niftypsycho/ortho-40percent/images/IMG_2475.JPG

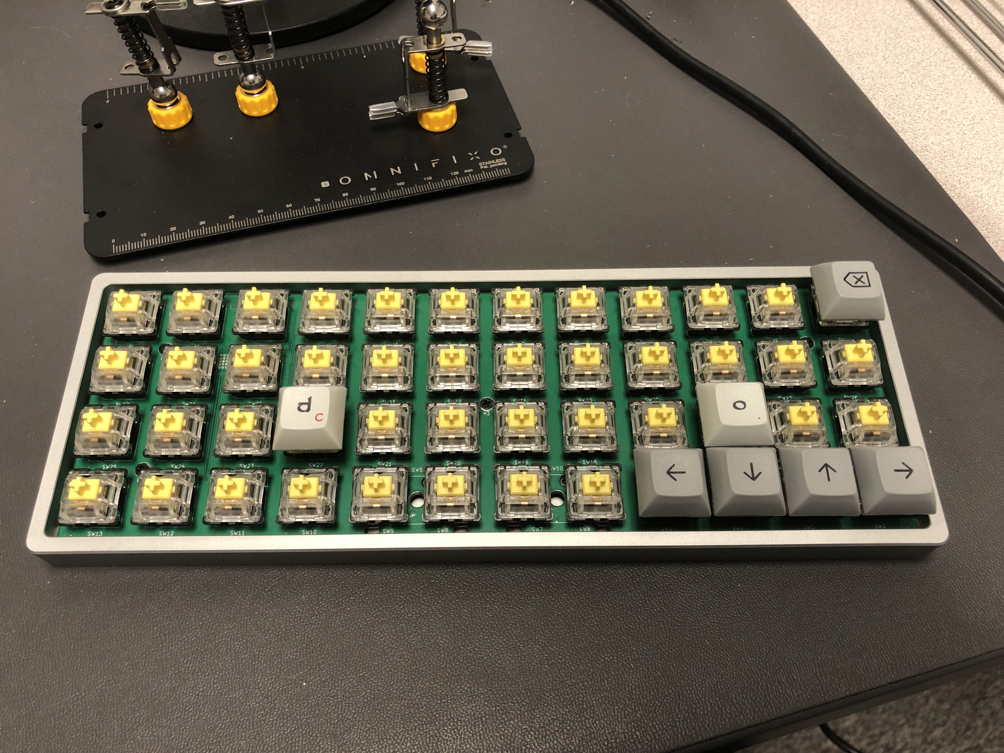
images/IMG_2475.JPG
