niftypsycho/ortho-40percent/images/IMG_2476.JPG

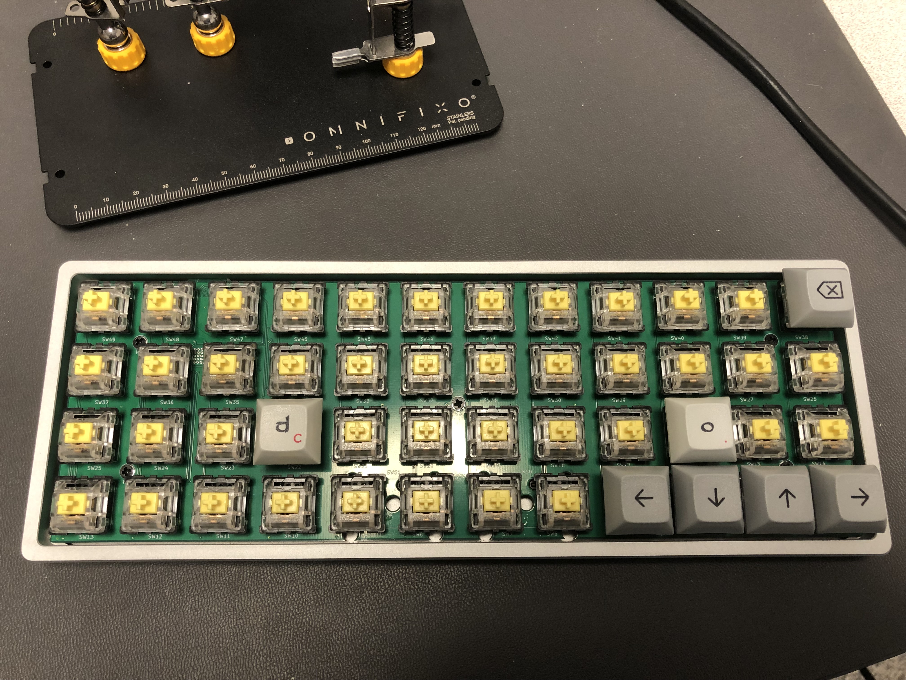
images/IMG_2476.JPG
