niftypsycho/ortho-40percent/images/IMG_2477.JPG

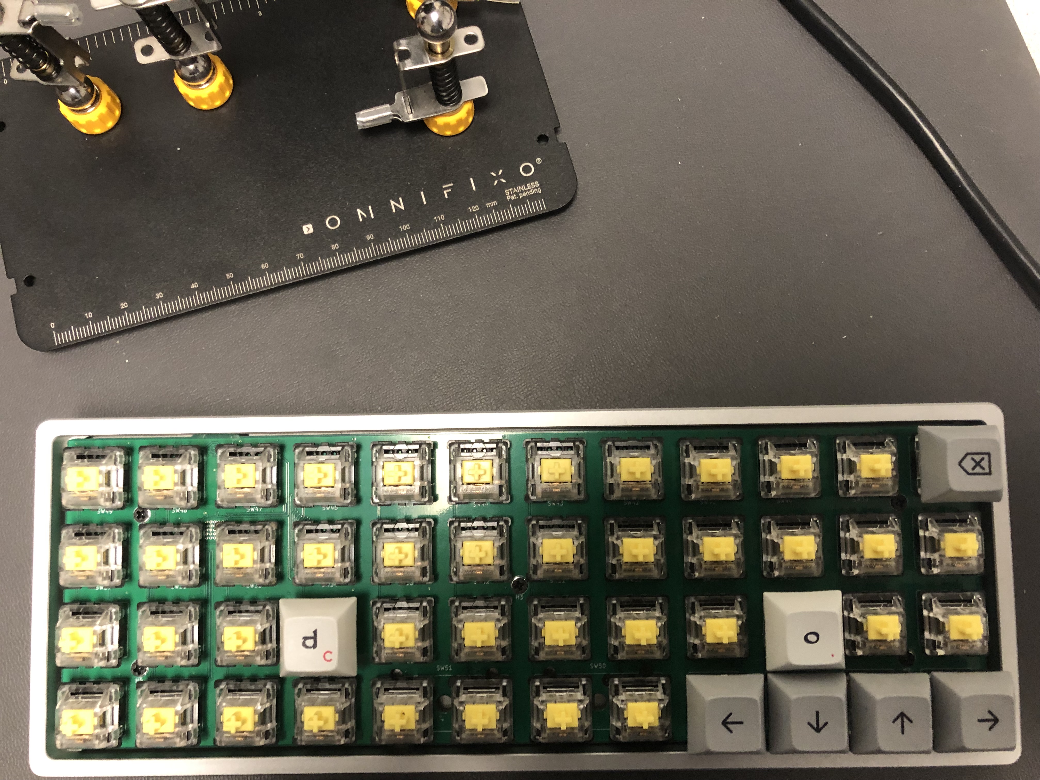
images/IMG_2477.JPG
