niftypsycho/ortho-40percent/images/IMG_2478.JPG

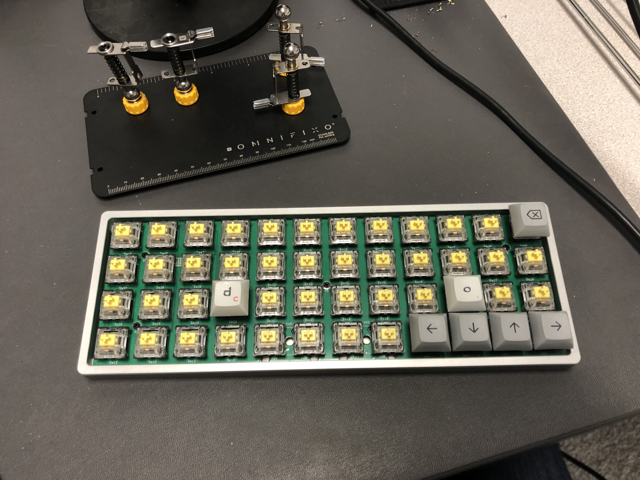
images/IMG_2478.JPG
