niftypsycho/ortho-40percent/images/IMG_2479.JPG

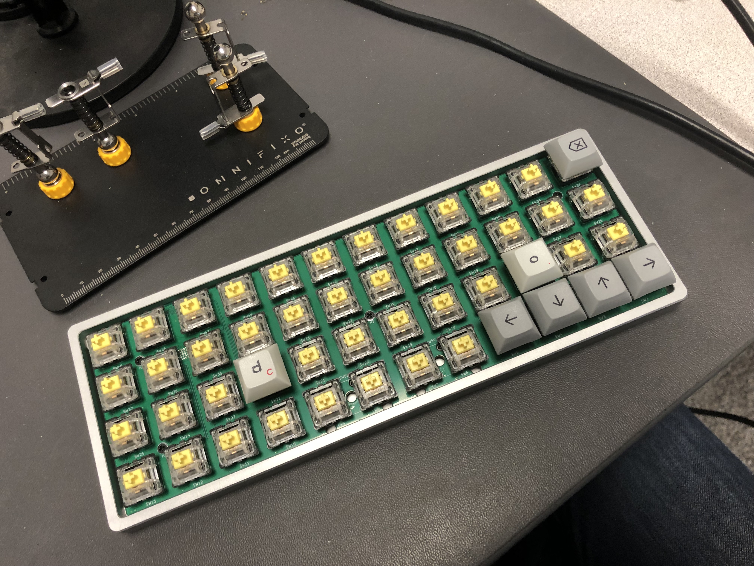
images/IMG_2479.JPG
