niftypsycho/ortho-40percent/images/IMG_2480.JPG

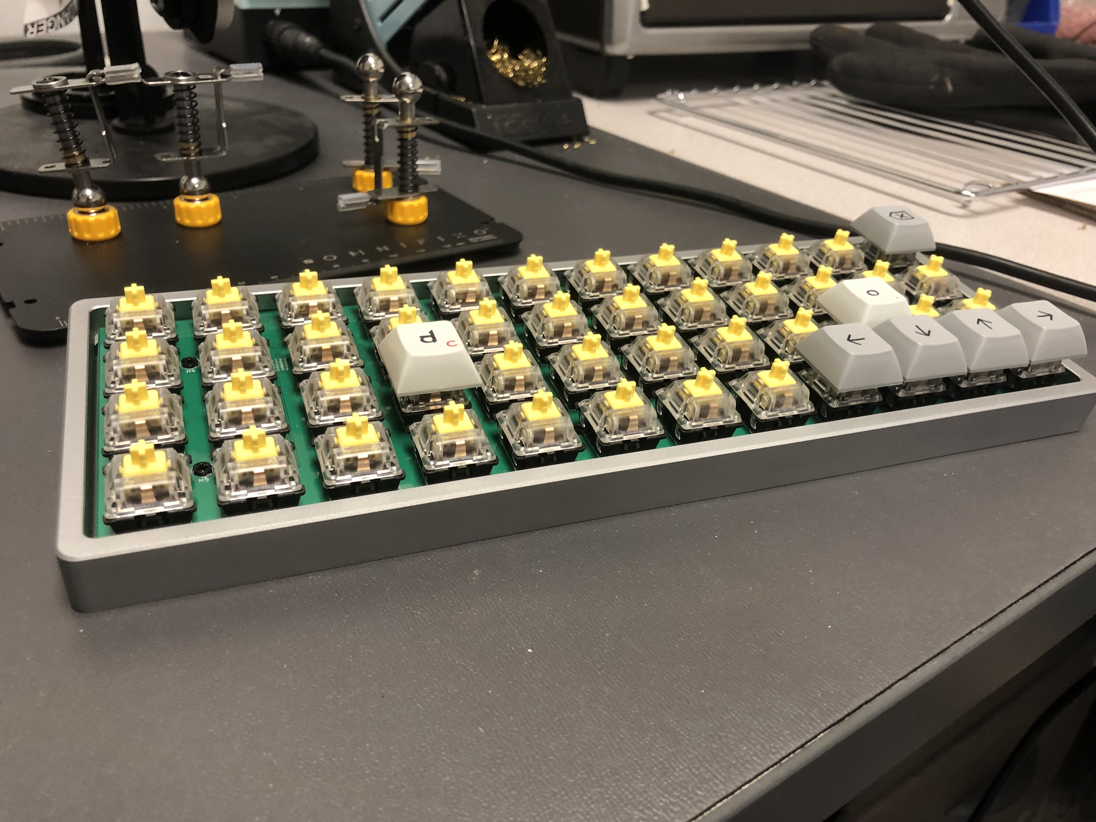
images/IMG_2480.JPG
