niftypsycho/ortho-40percent/images/IMG_2482.JPG

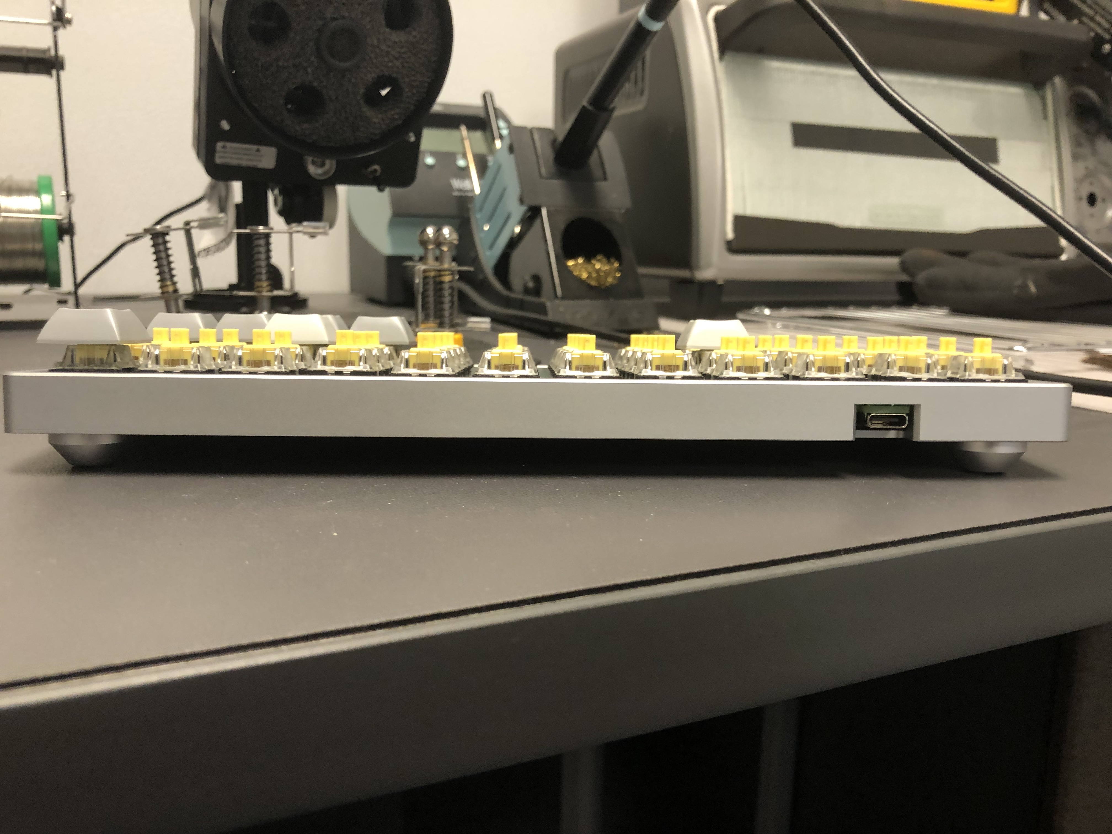
images/IMG_2482.JPG
